tomverbeure/fake_parallel_printer/examples/tds420a/tds420a_bmp_mono_0.bmp

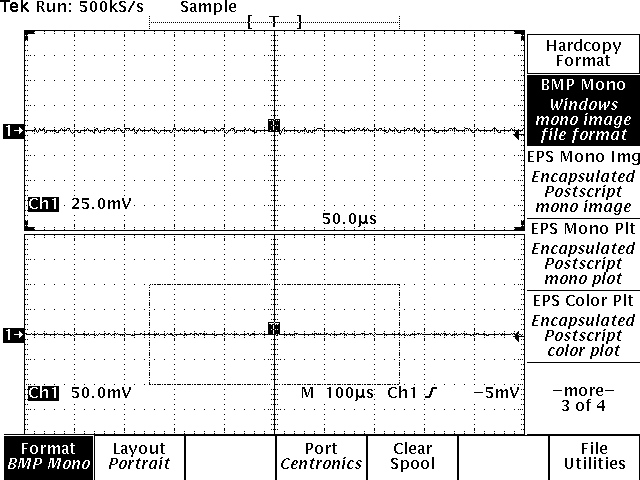
examples/tds420a/tds420a_bmp_mono_0.bmp
